DCHHV/DC26_HHV_RE/Firmware/DC26_HHV_RE_obfuscated/obfuscator.h

#include <SoftwareSerial.h>
#include <TinyWireM.h>
SoftwareSerial Serial(2,3);

#define Sp Serial.print
#define Spl Serial.println
#define pm pinMode
#define dw digitalWrite
#define ar analogRead
#define d delay

bool kp = false;
int lks = 1023;
uint8_t ke = 0;
uint8_t up[8] = {0};
bool wp = false;
uint8_t pw[8] = {1,4,4,3,1,2,1,2};
uint8_t EA = 80; uint8_t MA = 90;
uint8_t CV = 38; int i;

char s0[] = {0x57,0x65,0x6c,0x63,0x6f,0x6d,0x65,0x20,0x74,0x6f,0x20,0x74,0x68,0x65,0x20,0x44,0x43,0x20,0x32,0x36,0x20,0x48,0x48,0x56,0x20,0x43,0x68,0x61,0x6c,0x6c,0x65,0x6e,0x67,0x65,0x21,0x00};
char s1[] = {0x43,0x68,0x61,0x6c,0x6c,0x65,0x6e,0x67,0x65,0x20,0x32,0x3a,0x20,0x63,0x6f,0x6d,0x70,0x6c,0x65,0x74,0x65,0x00};
char s2[] = {0x46,0x6c,0x61,0x67,0x3a,0x20,0x30,0x68,0x5f,0x31,0x5f,0x72,0x33,0x6d,0x33,0x6d,0x62,0x33,0x72,0x5f,0x6e,0x30,0x77,0x21,0x00};
char s3[] = {0x43,0x68,0x61,0x6c,0x6c,0x65,0x6e,0x67,0x65,0x20,0x31,0x3a,0x00};
char s4[] = {0x45,0x6e,0x74,0x65,0x72,0x20,0x74,0x68,0x65,0x20,0x63,0x6f,0x72,0x72,0x65,0x63,0x74,0x20,0x70,0x61,0x73,0x73,0x63,0x6f,0x64,0x65,0x00};
char s5[] = {0x43,0x68,0x61,0x6c,0x6c,0x65,0x6e,0x67,0x65,0x20,0x31,0x3a,0x20,0x63,0x6f,0x6d,0x70,0x6c,0x65,0x74,0x65,0x00};
char s6[] = {0x46,0x6c,0x61,0x67,0x3a,0x20,0x68,0x33,0x79,0x5f,0x77,0x68,0x34,0x74,0x73,0x5f,0x74,0x33,0x68,0x5f,0x70,0x34,0x73,0x73,0x77,0x30,0x72,0x64,0x3f,0x00};
char s7[] = {0x4f,0x6f,0x70,0x73,0x21,0x20,0x57,0x72,0x6f,0x6e,0x67,0x20,0x70,0x61,0x73,0x73,0x63,0x6f,0x64,0x65,0x2c,0x20,0x74,0x72,0x79,0x20,0x61,0x67,0x61,0x69,0x6e,0x2e,0x00};

void s() {
  Serial.begin(9600);
  TinyWireM.begin();  // initialize I2C lib
  delay(100);
}
byte rE(int deviceaddress, unsigned int eeaddress ) {
  byte rdata = 0xFF;
  TinyWireM.beginTransmission(deviceaddress);
  TinyWireM.send((int)(eeaddress >> 8));   // MSB
  TinyWireM.send((int)(eeaddress & 0xFF)); // LSB
  TinyWireM.endTransmission();
  TinyWireM.requestFrom(deviceaddress,1);
  if (TinyWireM.available()) rdata = TinyWireM.receive();
  return rdata;
}
bool cE(){byte r=rE(EA,MA);if(r==CV){return 1;}return 0;}
